kulmn/ethernet_2granit/all/include/buffer.h

/*! \file buffer.h \brief Multipurpose byte buffer structure and methods. */
//*****************************************************************************
//
// File Name	: 'buffer.h'
// Title		: Multipurpose byte buffer structure and methods
// Author		: Pascal Stang - Copyright (C) 2001-2002
// Created		: 9/23/2001
// Revised		: 11/16/2002
// Version		: 1.1
// Target MCU	: any
// Editor Tabs	: 4
//
///	\ingroup general
/// \defgroup buffer Circular Byte-Buffer Structure and Function Library (buffer.c)
/// \code #include "buffer.h" \endcode
/// \par Overview
///		This byte-buffer structure provides an easy and efficient way to store
///		and process a stream of bytes.� You can create as many buffers as you
///		like (within memory limits), and then use this common set of functions to
///		access each buffer.� The buffers are designed for FIFO�operation (first
///		in, first out).� This means that the first byte you put in the buffer
///		will be the first one you get when you read out the buffer.� Supported
///		functions include buffer initialize, get byte from front of buffer, add
///		byte to end of buffer, check if buffer is full, and flush buffer.� The
///		buffer uses a circular design so no copying of data is ever necessary.
///		This buffer is not dynamically allocated, it has a user-defined fixed
///		maximum size.� This buffer is used in many places in the avrlib code.
//
// This code is distributed under the GNU Public License
//		which can be found at http://www.gnu.org/licenses/gpl.txt
//
//*****************************************************************************
//@{

#ifndef BUFFER_H
#define BUFFER_H

#include <stdint.h>


#ifdef USE_FREE_RTOS
// FreeRTOS include
#include "FreeRTOS.h"
#include "task.h"
#include "queue.h"

#define CRITICAL_SECTION_START	taskENTER_CRITICAL();
#define CRITICAL_SECTION_END	taskEXIT_CRITICAL();

#else

#define CRITICAL_SECTION_START	cm_disable_interrupts();
#define CRITICAL_SECTION_END		cm_enable_interrupts();

#endif


typedef enum { BUFFER_RESULT_OK, BUFFER_RESULT_ERROR } BUFFER_Result;

//! cBuffer structure
typedef struct struct_cBuffer
{
	uint8_t *dataptr;			///< the physical memory address where the buffer is stored
	uint16_t size;			///< the allocated size of the buffer
	uint16_t datalength;		///< the length of the data currently in the buffer
	uint16_t dataindex;		///< the index into the buffer where the data starts
} cBuffer;

// function prototypes

//! initialize a buffer to start at a given address and have given size
void	bufferInit(cBuffer* buffer, uint8_t *start, uint16_t size);

//! get the first byte from the front of the buffer
uint8_t	bufferGetFromFront(cBuffer* buffer);

//! dump (discard) the first numbytes from the front of the buffer
void	bufferDumpFromFront(cBuffer* buffer, uint16_t numbytes);

//! get a byte at the specified index in the buffer (kind of like array access)
// ** note: this does not remove the byte that was read from the buffer
uint8_t	bufferGetAtIndex(cBuffer* buffer, uint16_t index);

//! add a byte to the end of the buffer
BUFFER_Result	bufferAddToEnd(cBuffer* buffer, uint8_t data);

//! check if the buffer is full/not full (returns zero value if full)
uint16_t	bufferIsNotFull(cBuffer* buffer);

//! flush (clear) the contents of the buffer
void	bufferFlush(cBuffer* buffer);

#endif
//@}
