kulmn/ethernet_2granit/all/include/usart_hl.h

/*
 * usart_hl.h
 *
 *  Created on: 16 ����. 2016 �.
 *      Author: kulish_y
 */

#ifndef INCLUDE_USART_HAL_H_
#define INCLUDE_USART_HAL_H_

#include <stdint.h>
#include <libopencm3/stm32/usart.h>
#include "buffer.h"

//#define USE_USART1
#define USE_USART2

typedef enum { USART_RESULT_OK, USART_RESULT_ERROR } USART_Result;


typedef struct
{
	uint32_t		usart;
	uint16_t		baudrate;
	uint8_t		rx_buf_size;
	uint8_t		tx_buf_size;
	uint8_t 		*rx_buf_ptr;
	uint8_t 		*tx_buf_ptr;
	cBuffer 		rx_buf;				///< uart receive buffer
	cBuffer 		tx_buf;				///< uart transmit buffer
}USART_HAL;




void uart_init(USART_HAL *uart);


//! Gets a single byte from the uart receive buffer.
/// Returns the byte, or -1 if no byte is available (getchar-style).
int uartGetByte(USART_HAL *uart);

//! Gets a single byte from the uart receive buffer.
/// Function returns TRUE if data was available, FALSE if not.
/// Actual data is returned in variable pointed to by "data".
/// Example usage:
/// \code
/// char myReceivedByte;
/// uartReceiveByte( &myReceivedByte );
/// \endcode
USART_Result usart_hl_get_byte(USART_HAL *uart, uint8_t* data);



//! Flushes (deletes) all data from receive buffer.
///
void uartFlushReceiveBuffer(USART_HAL *uart);


// Buffered send a byte via the uart using interrupt control.
USART_Result usart_hl_send(USART_HAL *uart, uint8_t data);

// Buffered send a string via the uart using interrupt control.
USART_Result usart_hl_send_str(USART_HAL *uart, uint8_t* str);



//! Sends a block of data via the uart using interrupt control.
/// \param buffer	pointer to data to be sent
///	\param nBytes	length of data (number of bytes to sent)
uint8_t  uartSendBuffer(char *buffer, uint16_t nBytes);

#endif /* INCLUDE_USART_HAL_H_ */
